KLPraktikum/Code/Arduino/LEDCalibrator/LEDCalibrator.ino

#include <FastLED.h>

FASTLED_USING_NAMESPACE

// FastLED "100-lines-of-code" demo reel, showing just a few 
// of the kinds of animation patterns you can quickly and easily 
// compose using FastLED.  
//
// This example also shows one easy way to define multiple 
// animations patterns and have them automatically rotate.
//
// -Mark Kriegsman, December 2014

#if defined(FASTLED_VERSION) && (FASTLED_VERSION < 3001000)
#warning "Requires FastLED 3.1 or later; check github for latest code."
#endif

#define DATA_PIN    9
#define CLK_PIN   10
#define LED_TYPE    APA102
#define COLOR_ORDER RGB
#define NUM_LEDS    189
CRGB leds[NUM_LEDS];

#define BRIGHTNESS          96
#define FRAMES_PER_SECOND  120

void setup() {
  Serial.begin(115200);
  
  // tell FastLED about the LED strip configuration
  //FastLED.addLeds<LED_TYPE,DATA_PIN,COLOR_ORDER>(leds, NUM_LEDS).setCorrection(TypicalLEDStrip);
  //FastLED.addLeds<LED_TYPE,DATA_PIN,CLK_PIN,COLOR_ORDER>(leds, NUM_LEDS).setCorrection(TypicalLEDStrip);
  FastLED.addLeds<LED_TYPE, DATA_PIN, CLK_PIN, COLOR_ORDER>(leds, NUM_LEDS).setCorrection(TypicalLEDStrip);
  // set master brightness control
  FastLED.setBrightness(BRIGHTNESS);
}

  
void loop()
{
  if(Serial.available())  {
    leds[Serial.parseInt()] = CRGB::HotPink;
        while(Serial.available()) {
      Serial.read();
    }
    FastLED.show(); 
  }
}
